TomoGraphics/Hol3Drs/STL/Mouse.Lymphnode.Samplechanger.stl

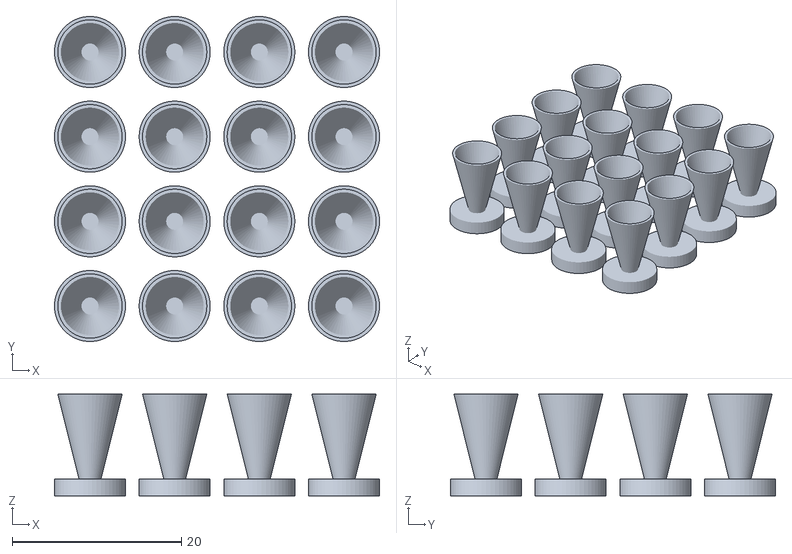
[picture p16: CAD file, 2020-12-01]
STL/Mouse.Lymphnode.Samplechanger.stl
38.4 x 38.4 x 12.0
