TomoGraphics/Hol3Drs/STL/Rat.Heart.Samplechanger.stl

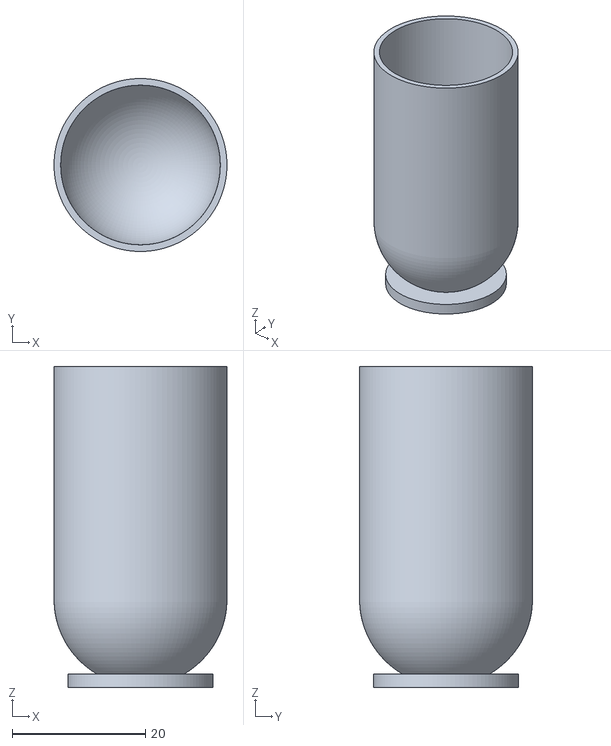
[picture p17: CAD file, 2020-11-02]
STL/Rat.Heart.Samplechanger.stl
26.0 x 26.0 x 48.2
