TomoGraphics/Hol3Drs/STL/tooth_holder3.stl

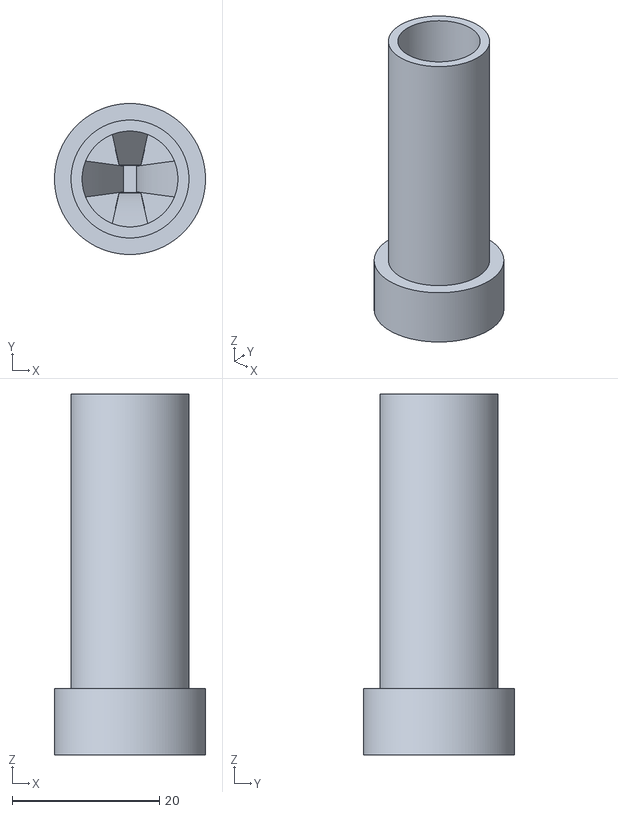
[picture p18: CAD file, 2020-09-04]
STL/tooth_holder3.stl
20.5 x 20.5 x 49.0
