TomoGraphics/Hol3Drs/STL/Zebrafish.Heart.Samplechanger.stl

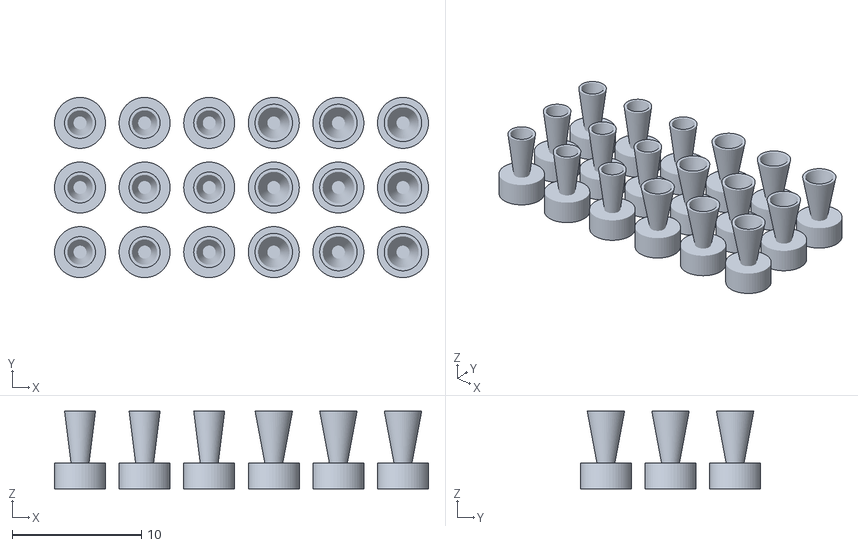
[picture p19: CAD file, 2020-09-04]
STL/Zebrafish.Heart.Samplechanger.stl
29.0 x 13.9 x 6.00
