TomoGraphics/Hol3Drs/STL/Zebrafish.Samplechanger.stl

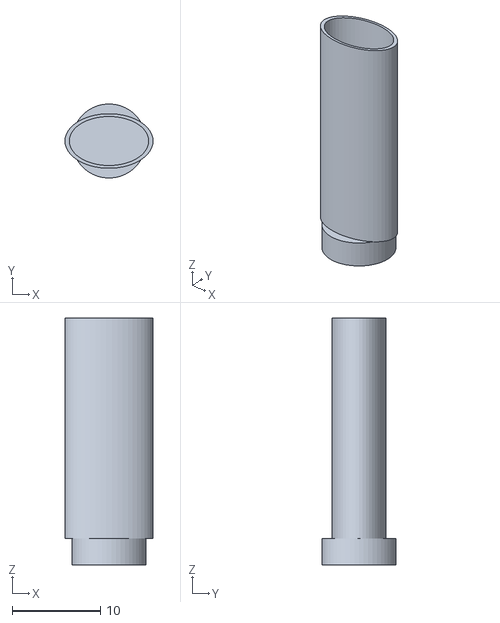
[picture p20: CAD file, 2020-09-04]
STL/Zebrafish.Samplechanger.stl
10.0 x 8.38 x 28.0
