TomoGraphics/Hol3Drs/STL/Zebrafish.Head.Samplechanger.stl

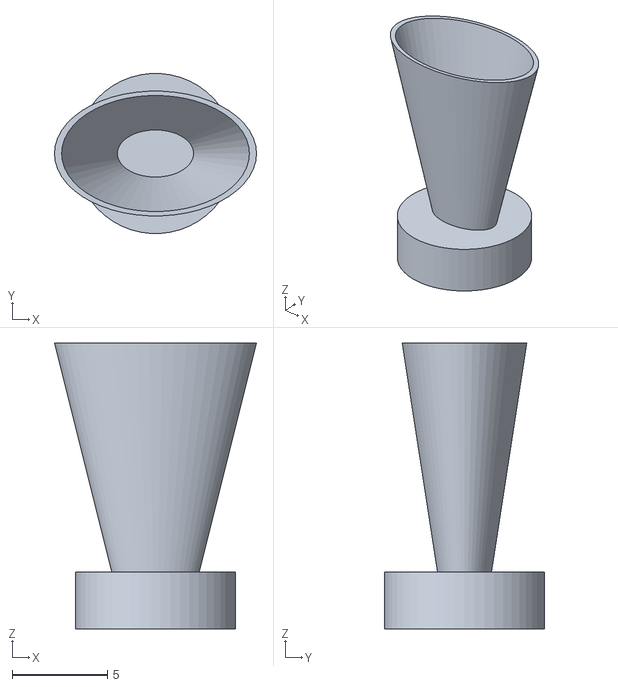
[picture p21: CAD file, 2020-09-04]
STL/Zebrafish.Head.Samplechanger.stl
10.6 x 8.38 x 15.0
