TomoGraphics/Hol3Drs/STL/Mouse.Heart.Wet.stl

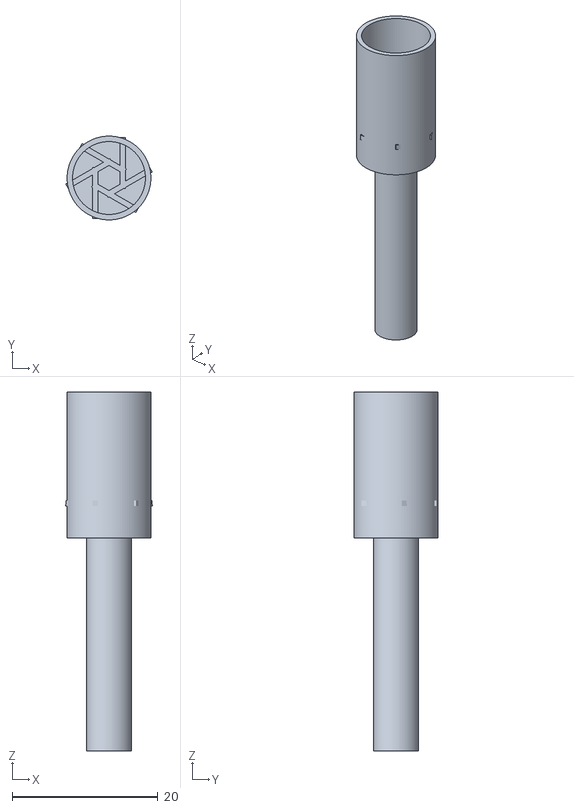
[picture p22: CAD file, 2020-02-14]
STL/Mouse.Heart.Wet.stl
11.9 x 11.5 x 49.2
