TomoGraphics/Hol3Drs/STL/Rat.Eye.stl

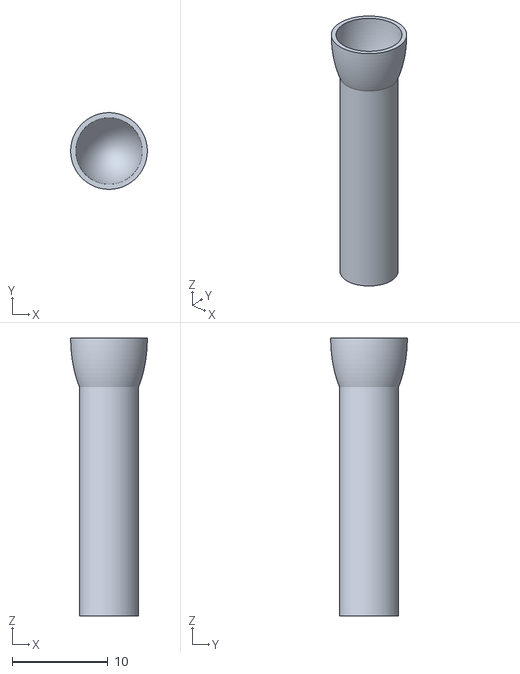
[picture p23: CAD file, 2020-02-14]
STL/Rat.Eye.stl
8.00 x 8.00 x 29.0
