TomoGraphics/Hol3Drs/STL/Zebrafish.stl

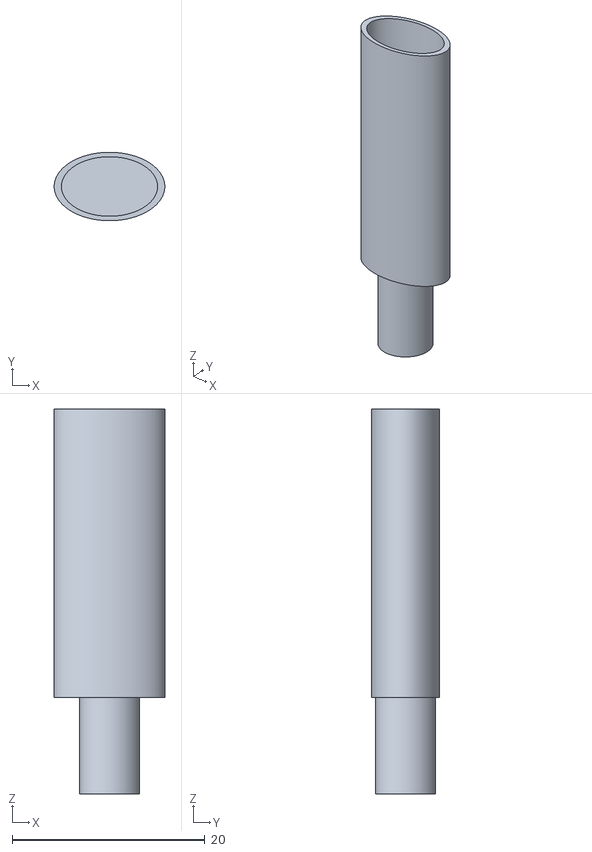
[picture p24: CAD file, 2020-02-14]
STL/Zebrafish.stl
11.5 x 7.11 x 40.0
