TomoGraphics/Hol3Drs/STL/FalconTubeHolder.stl

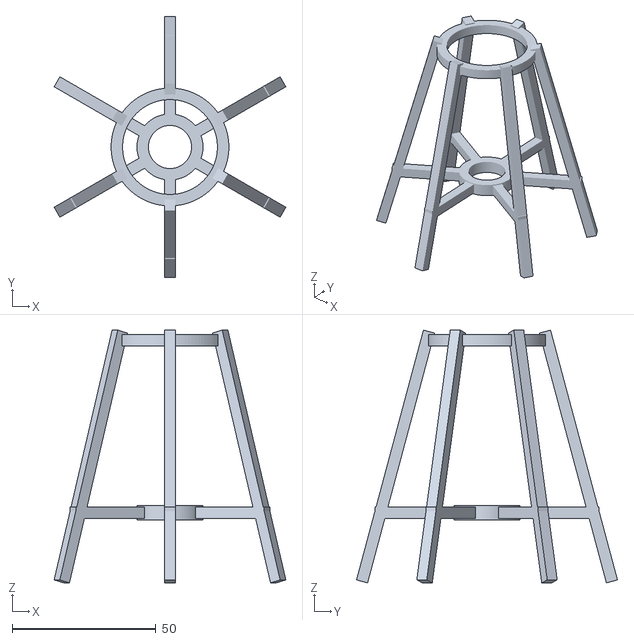
[picture p25: CAD file, 2020-02-14]
STL/FalconTubeHolder.stl
80.7 x 90.8 x 88.0
