TomoGraphics/Hol3Drs/STL/SampleHolderHolder.stl

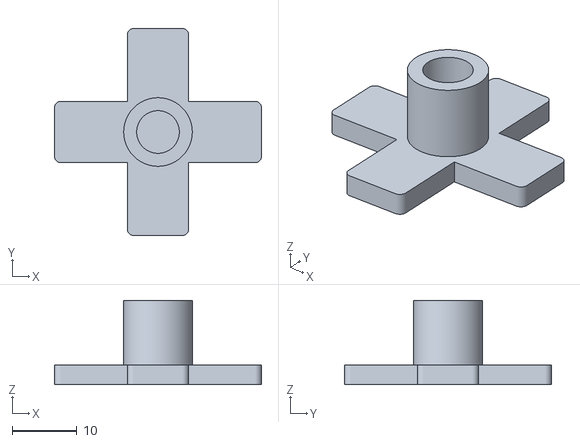
[picture p26: CAD file, 2019-06-11]
STL/SampleHolderHolder.stl
32.0 x 32.0 x 13.0
