TomoGraphics/Hol3Drs/STL/Mouse.Lung.Wet.stl

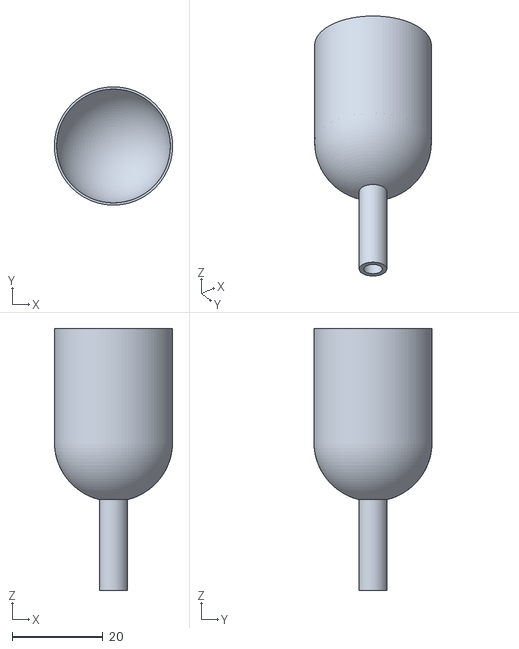
[picture p27: CAD file, 2019-06-11]
STL/Mouse.Lung.Wet.stl
26.0 x 26.0 x 57.6
