TomoGraphics/Hol3Drs/STL/Toothpick.stl

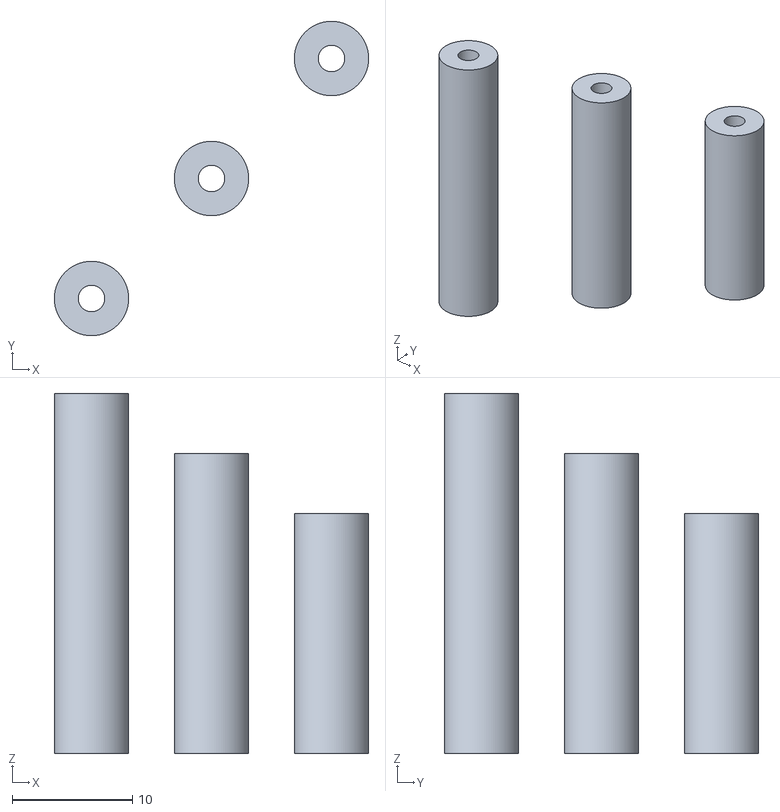
[picture p28: CAD file, 2019-06-11]
STL/Toothpick.stl
26.2 x 26.2 x 30.0
