TomoGraphics/Hol3Drs/STL/Mouse.Lung.Technovit.stl

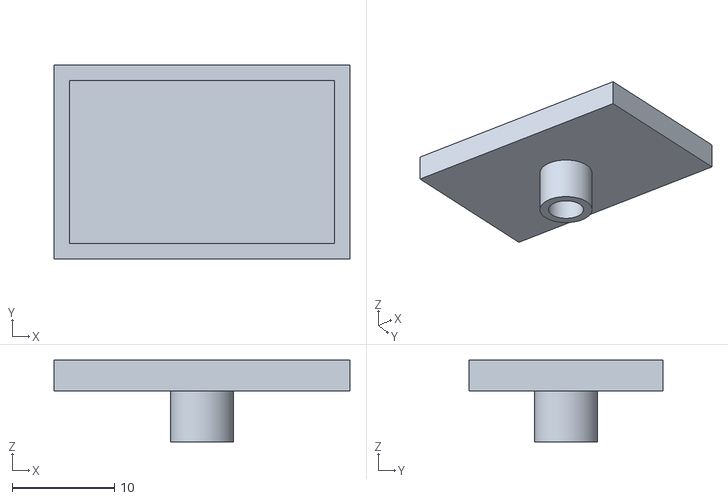
[picture p29: CAD file, 2019-06-11]
STL/Mouse.Lung.Technovit.stl
29.0 x 19.0 x 8.00
