TomoGraphics/Hol3Drs/STL/Rabbit.Retina.stl

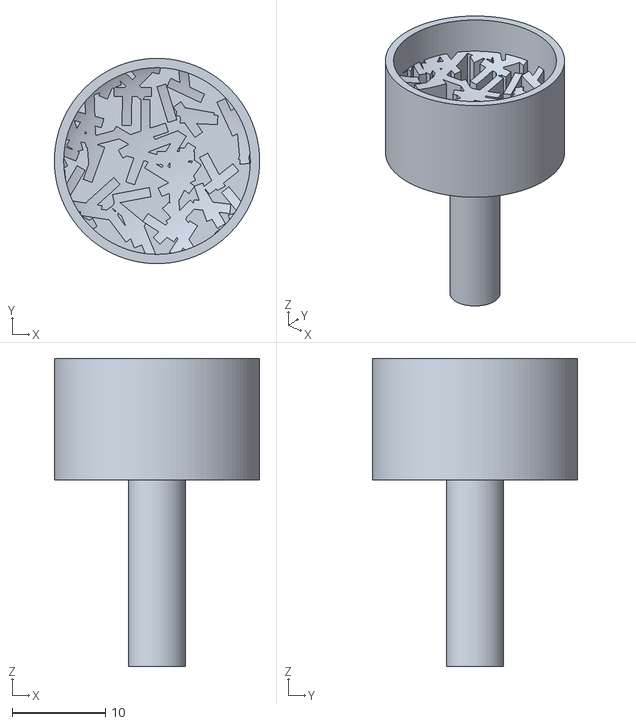
[picture p30: CAD file, 2018-11-12]
STL/Rabbit.Retina.stl
22.0 x 22.0 x 33.0
