TomoGraphics/Hol3Drs/STL/random_pins.stl

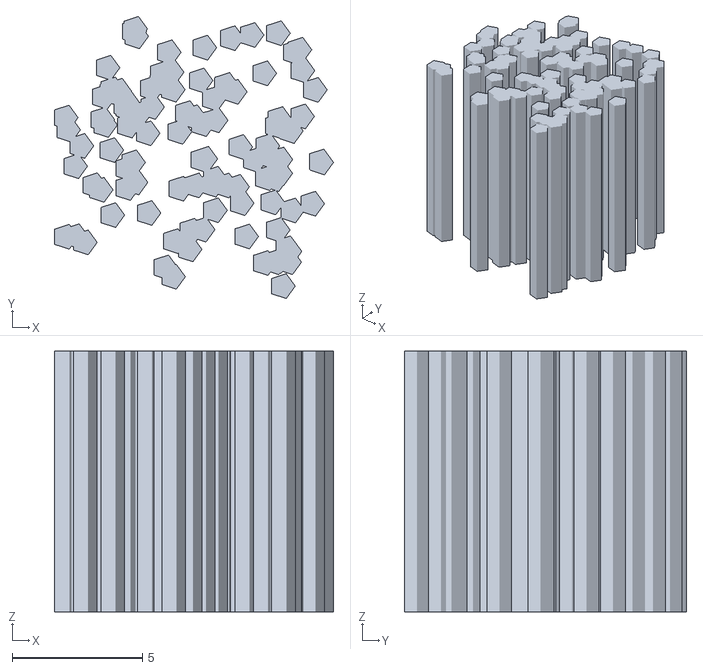
[picture p31: CAD file, 2018-08-20]
STL/random_pins.stl
10.7 x 10.8 x 10.0
