TomoGraphics/Hol3Drs/STL/Zebrafish.Head.stl

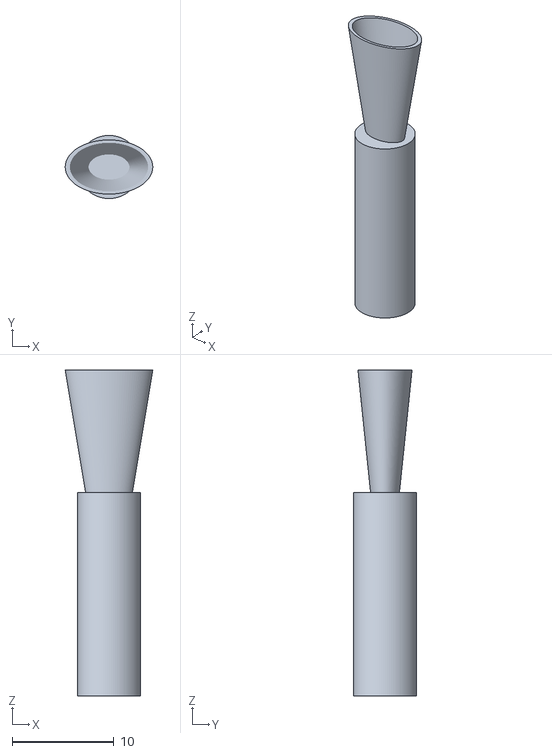
[picture p32: CAD file, 2018-03-21]
STL/Zebrafish.Head.stl
8.60 x 6.20 x 32.0
