TomoGraphics/Hol3Drs/STL/Mouse.Spine.stl

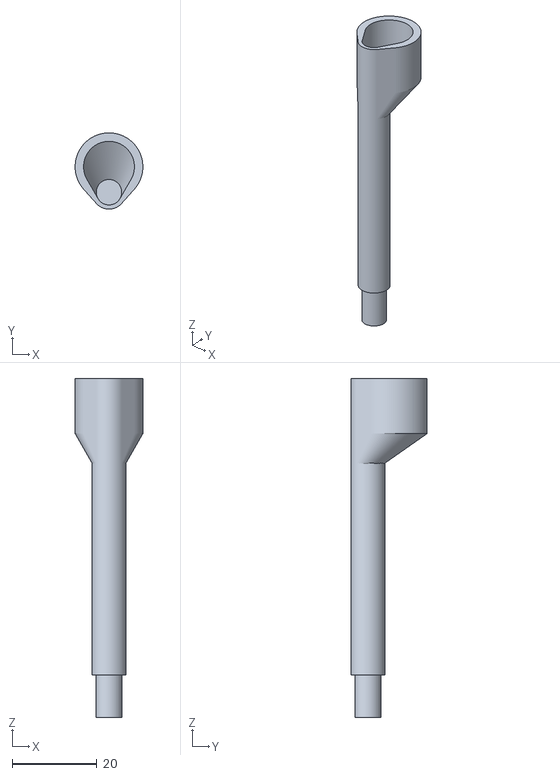
[picture p33: CAD file, 2018-03-21]
STL/Mouse.Spine.stl
16.0 x 18.0 x 80.0
