TomoGraphics/Hol3Drs/STL/Mouse.Lung.CriticallyPointDried.RUL.stl

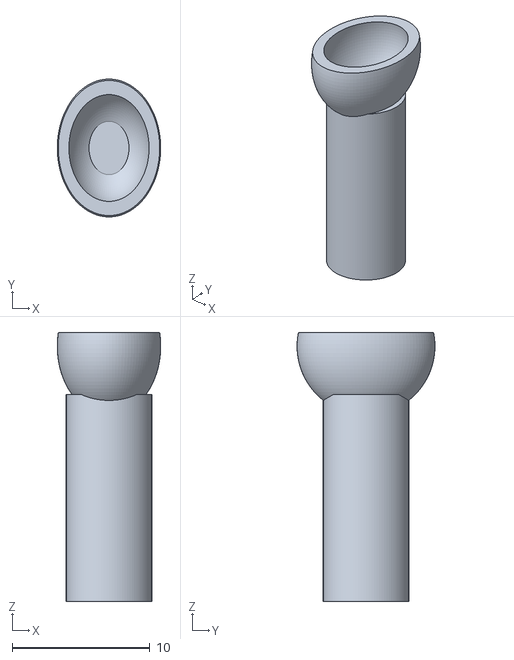
[picture p34: CAD file, 2018-03-21]
STL/Mouse.Lung.CriticallyPointDried.RUL.stl
7.50 x 10.00 x 19.5
