TomoGraphics/Hol3Drs/STL/Mouse.Tumors.Big.stl

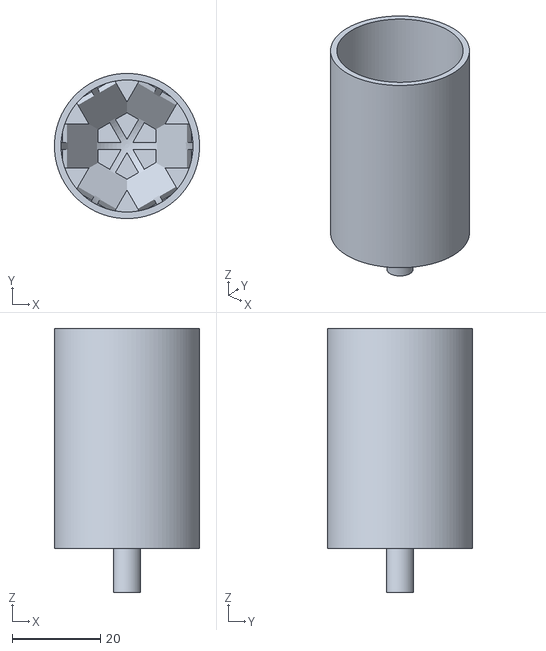
[picture p35: CAD file, 2018-03-21]
STL/Mouse.Tumors.Big.stl
33.0 x 33.0 x 60.0
