TomoGraphics/Hol3Drs/STL/Mouse.Lung.CriticallyPointDried.stl

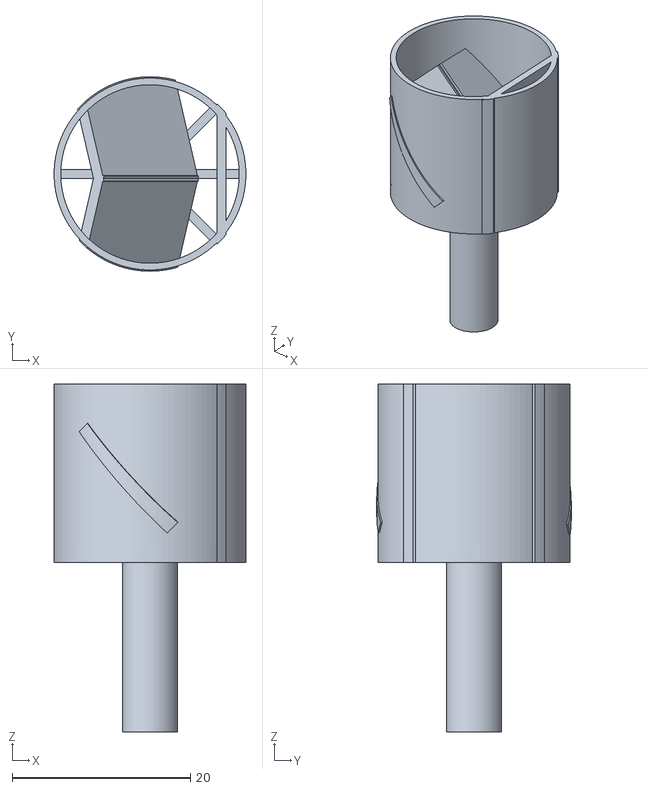
[picture p36: CAD file, 2018-03-21]
STL/Mouse.Lung.CriticallyPointDried.stl
21.5 x 21.8 x 39.0
