TomoGraphics/Hol3Drs/STL/Mouse.Eye.stl

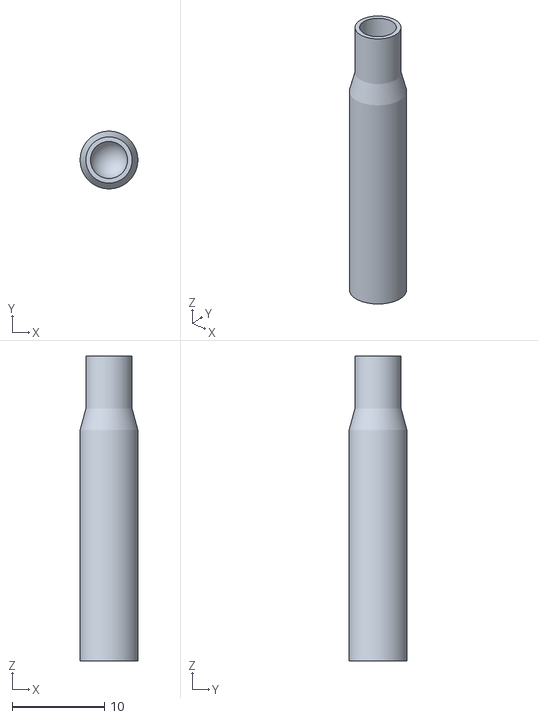
[picture p37: CAD file, 2018-03-21]
STL/Mouse.Eye.stl
6.25 x 6.25 x 33.0
