TomoGraphics/Hol3Drs/STL/Rat.Brain.stl

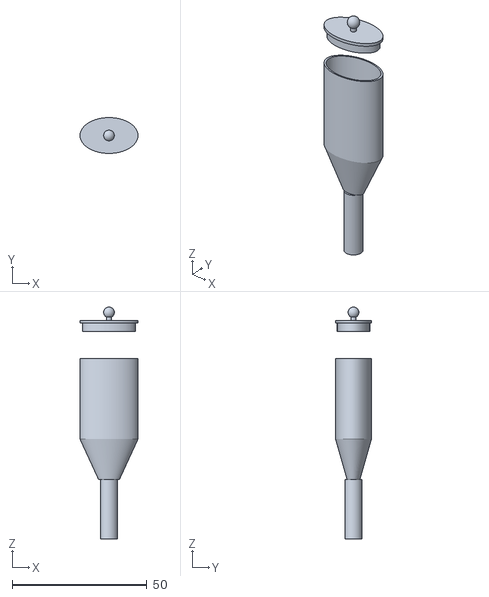
[picture p38: CAD file, 2018-03-21]
STL/Rat.Brain.stl
21.5 x 13.3 x 86.0
