TomoGraphics/Hol3Drs/STL/Wooblock.stl

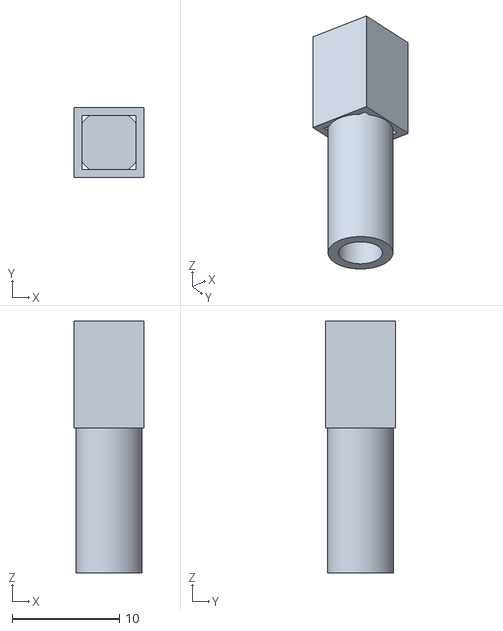
[picture p39: CAD file, 2018-03-21]
STL/Wooblock.stl
6.50 x 6.50 x 23.5
