TomoGraphics/Hol3Drs/STL/Mouse.Brain.stl

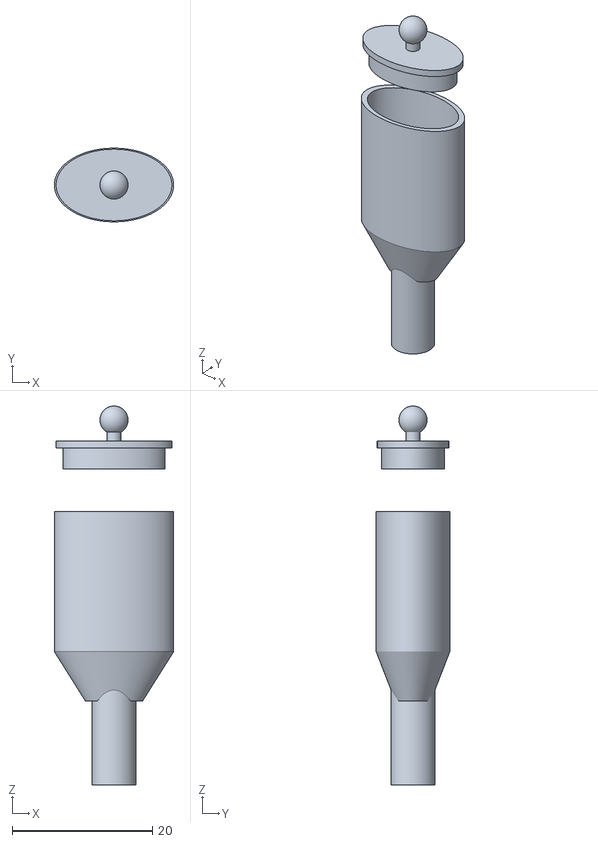
[picture p40: CAD file, 2018-03-21]
STL/Mouse.Brain.stl
17.0 x 10.5 x 54.0
