TomoGraphics/Hol3Drs/STL/Zebrafish.Heart.stl

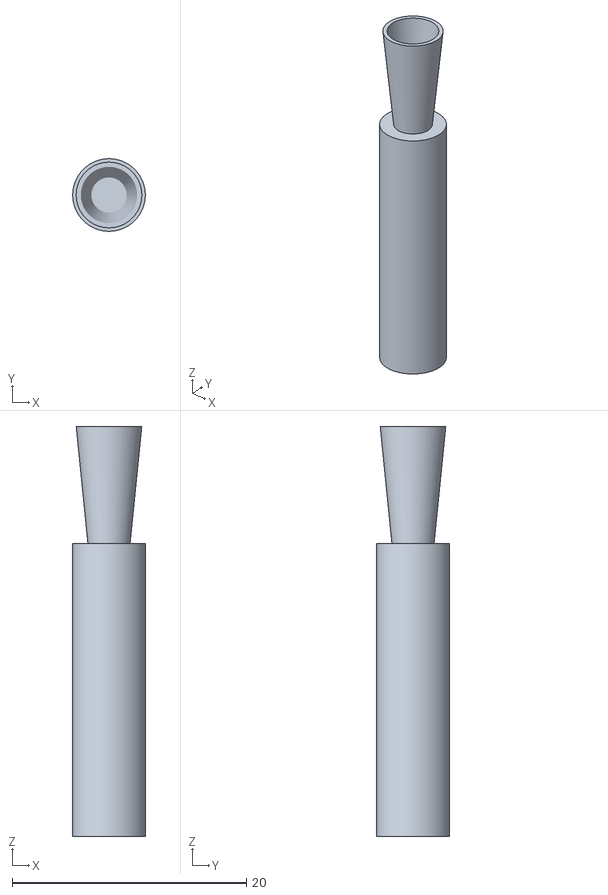
[picture p41: CAD file, 2018-03-21]
STL/Zebrafish.Heart.stl
6.20 x 6.20 x 35.0
