TomoGraphics/Hol3Drs/STL/Biopsypunch.stl

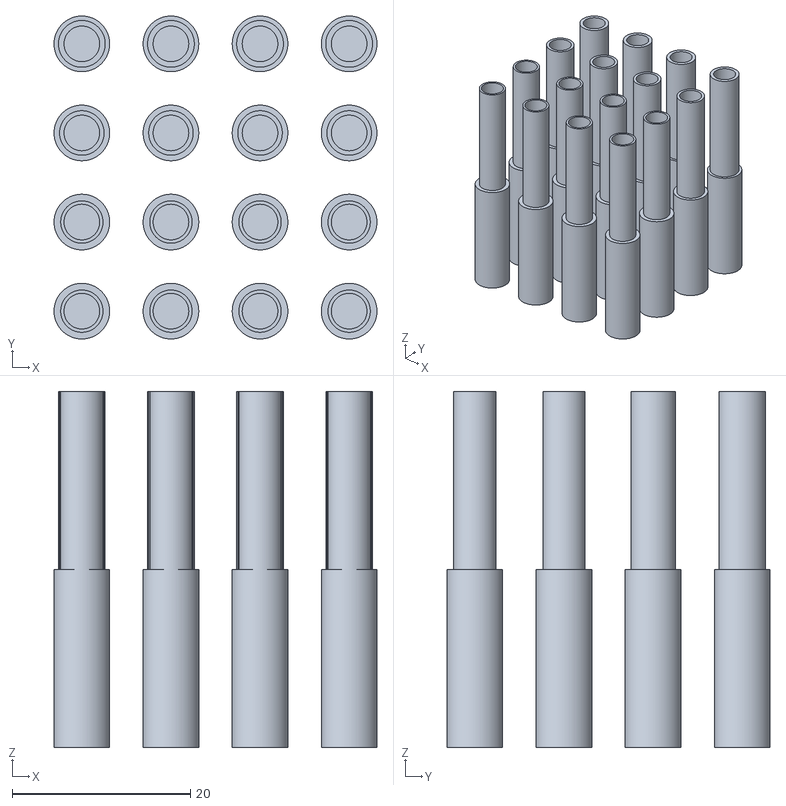
[picture p42: CAD file, 2018-03-21]
STL/Biopsypunch.stl
36.2 x 36.2 x 40.0
