TomoGraphics/Hol3Drs/STL/GenericSampleHolders.stl

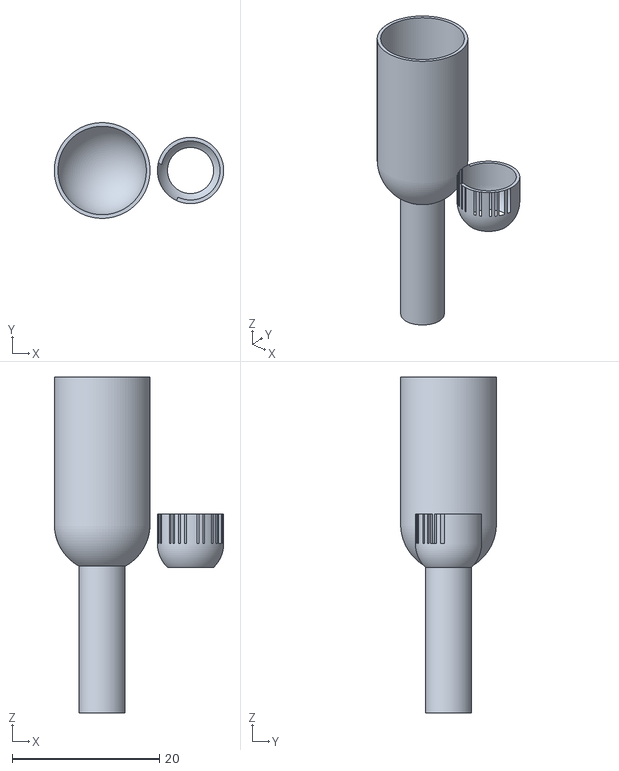
[picture p43: CAD file, 2018-03-21]
STL/GenericSampleHolders.stl
23.0 x 13.0 x 45.6
