TomoGraphics/Hol3Drs/STL/Needle.stl

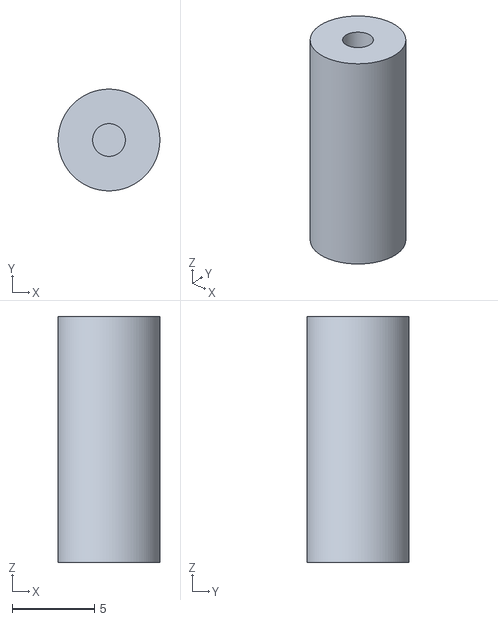
[picture p44: CAD file, 2018-03-21]
STL/Needle.stl
6.20 x 6.20 x 15.0
